1Bitsy/1bitsy-hardware/doc/1bitsy_v1_0_legend.graffle/image2.png

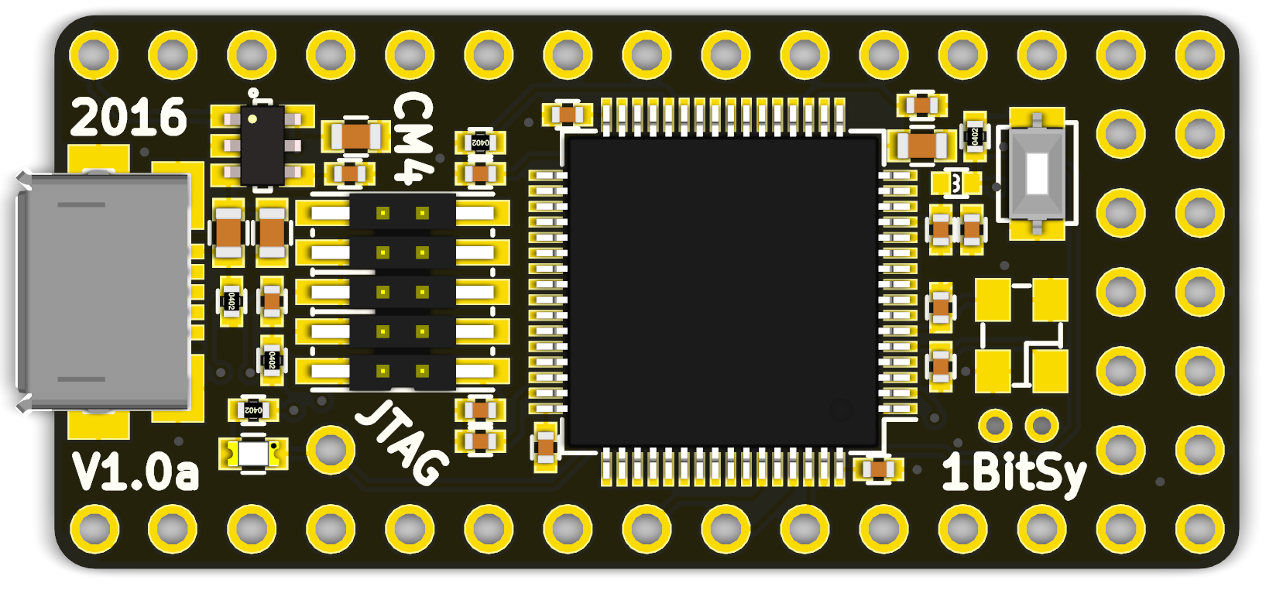
doc/1bitsy_v1_0_legend.graffle/image2.png
