1Bitsy/1bitsy-hardware/doc/1bitsy_v1_0b_legend2.graffle/image4.png

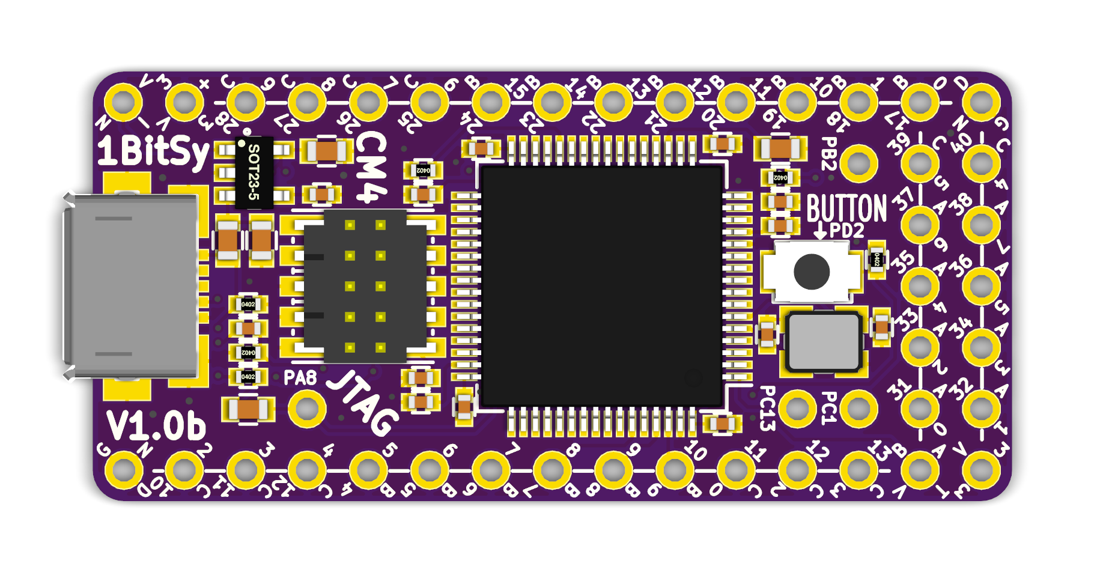
doc/1bitsy_v1_0b_legend2.graffle/image4.png
