1Bitsy/1bitsy-hardware/doc/1bitsy_v1_0b_legend.png

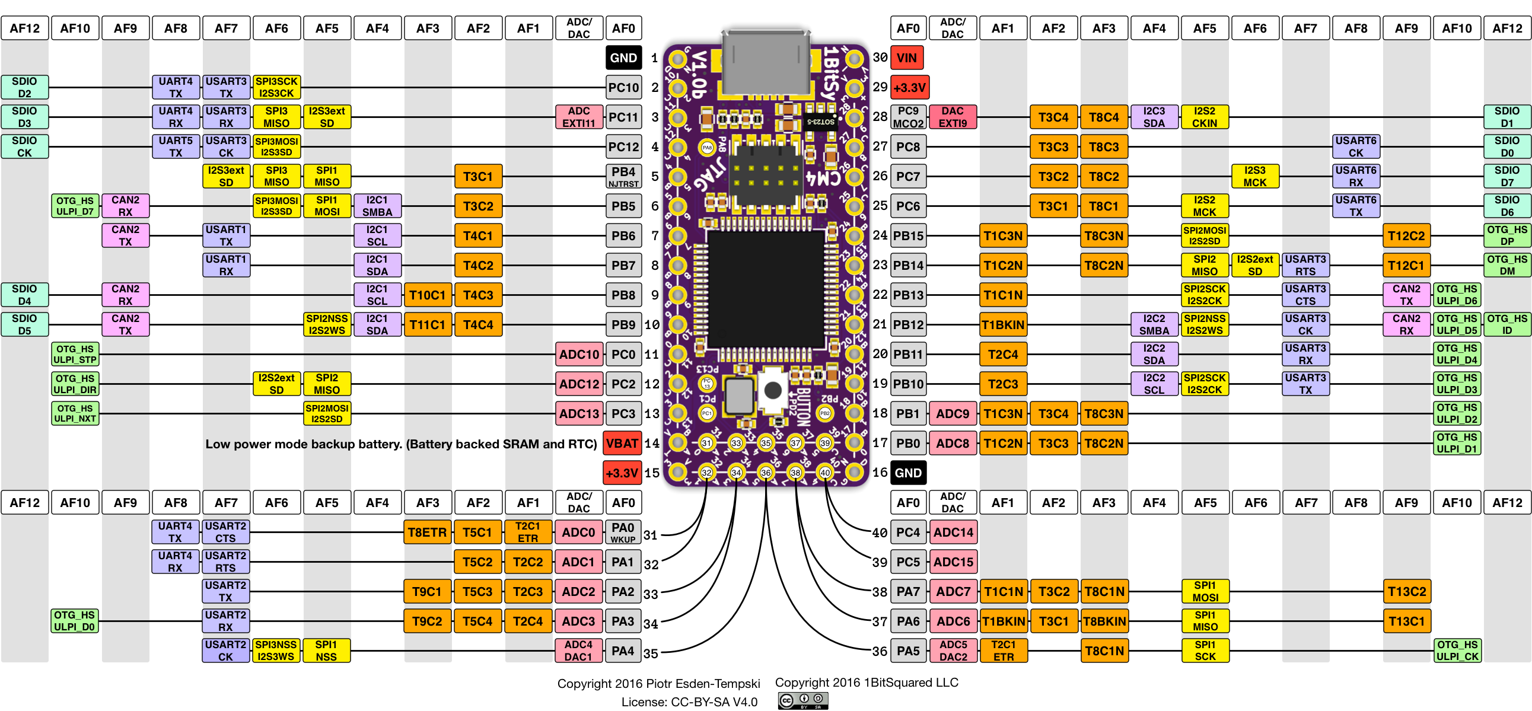
doc/1bitsy_v1_0b_legend.png
