1Bitsy/1bitsy-hardware/doc/1bitsy_v1_0d_legend2.graffle/image5.png

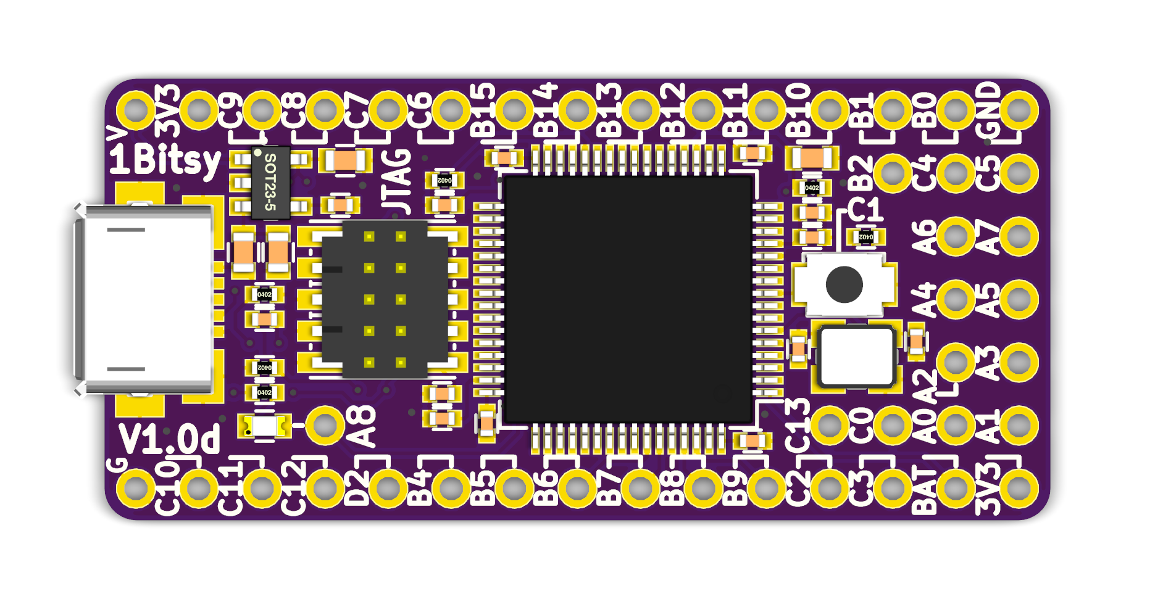
doc/1bitsy_v1_0d_legend2.graffle/image5.png
