1Bitsy/1bitsy-hardware/doc/1bitsy_v1_0d_legend_back.graffle/image9.png

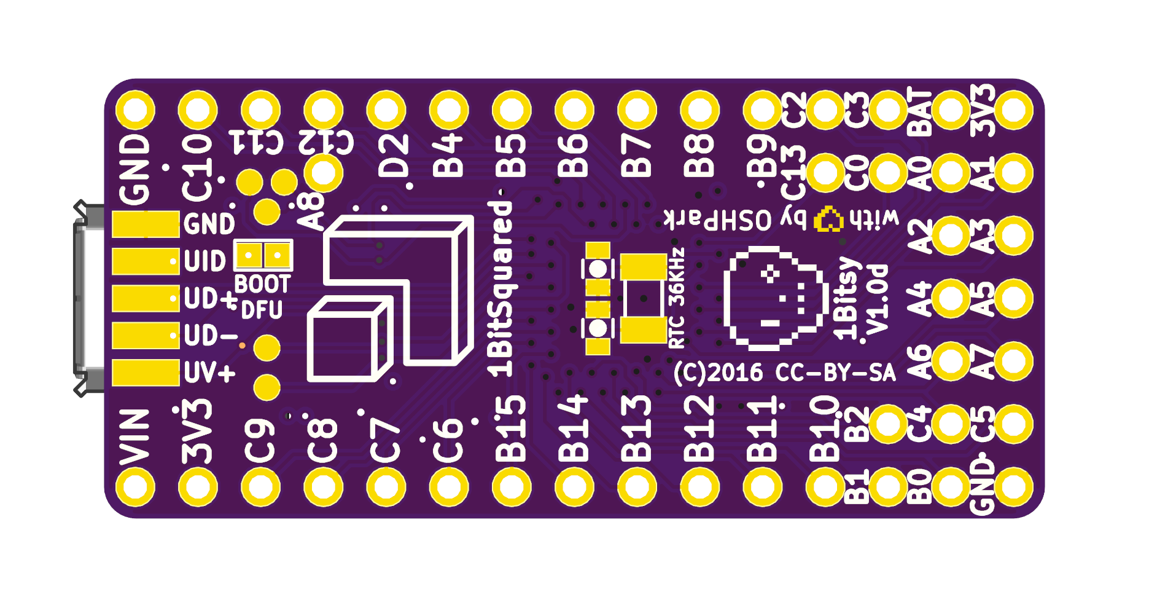
doc/1bitsy_v1_0d_legend_back.graffle/image9.png
